tominabox1/BLe-Chiffre/KiCad/image0.jpg

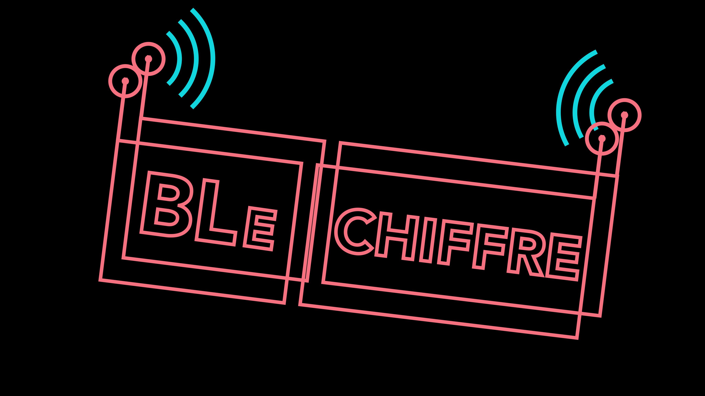
KiCad/image0.jpg
